SovietCoffe404/Hack-Pad-V2-HC-project/firmware/src/display.h

#pragma once
#include <Arduino.h>
#include <Adafruit_GFX.h>
#include <Adafruit_SSD1351.h>

void display_init();
void display_show_home();                 // home screen (custom text)
void display_set_ble_status(bool connected); // status dot, top right
void display_show_image_rgb565(const uint16_t *pixels); // 128x128 from the PC app
void display_show_text(const char *msg, uint16_t color);
Adafruit_SSD1351 &display_raw();           // direct access for the minigame
